papabur/sE1X-10mm/sE1X X Axis Printed Parts/OpenX Carriage (sE1X_15)(1of3).SLDPRT

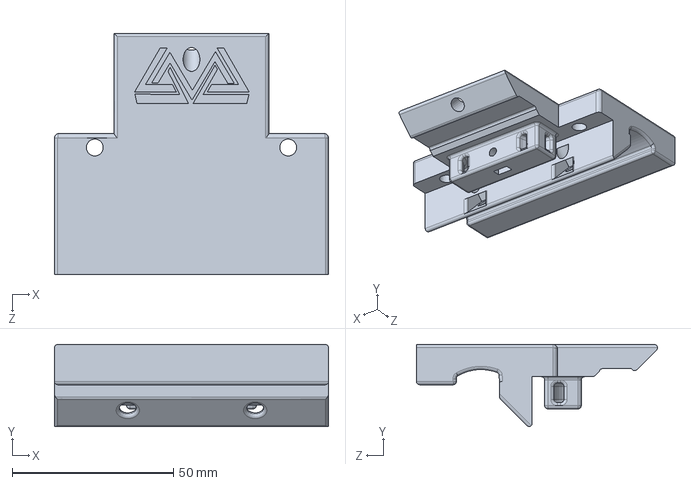
[picture p15: CAD file, 2015-11-26]
sE1X X Axis Printed Parts/OpenX Carriage (sE1X_15)(1of3).SLDPRT
85.0 x 25.5 x 74.8 mm
