papabur/sE1X-10mm/sE1X Y Axis Printed Parts/Printer Supports -sE1X.SLDPRT

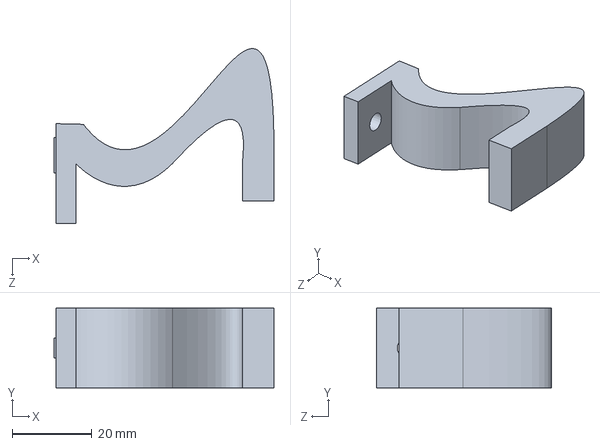
[picture p16: CAD file, 2015-11-09]
sE1X Y Axis Printed Parts/Printer Supports -sE1X.SLDPRT
55.1 x 20.0 x 43.8 mm
