papabur/sE1X-10mm/sE1X Z Axis Printed Parts/5mm threaded rod.SLDPRT

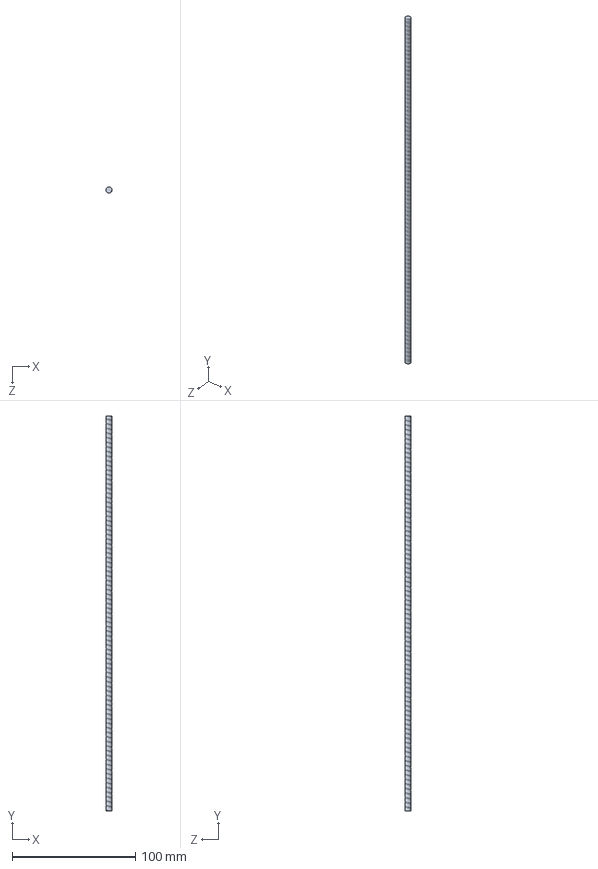
[picture p17: CAD file, 2015-11-19]
sE1X Z Axis Printed Parts/5mm threaded rod.SLDPRT
5.00 x 321.1 x 5.00 mm
