papabur/sE1X-10mm/ChrisM21 10mm star fit.SLDPRT

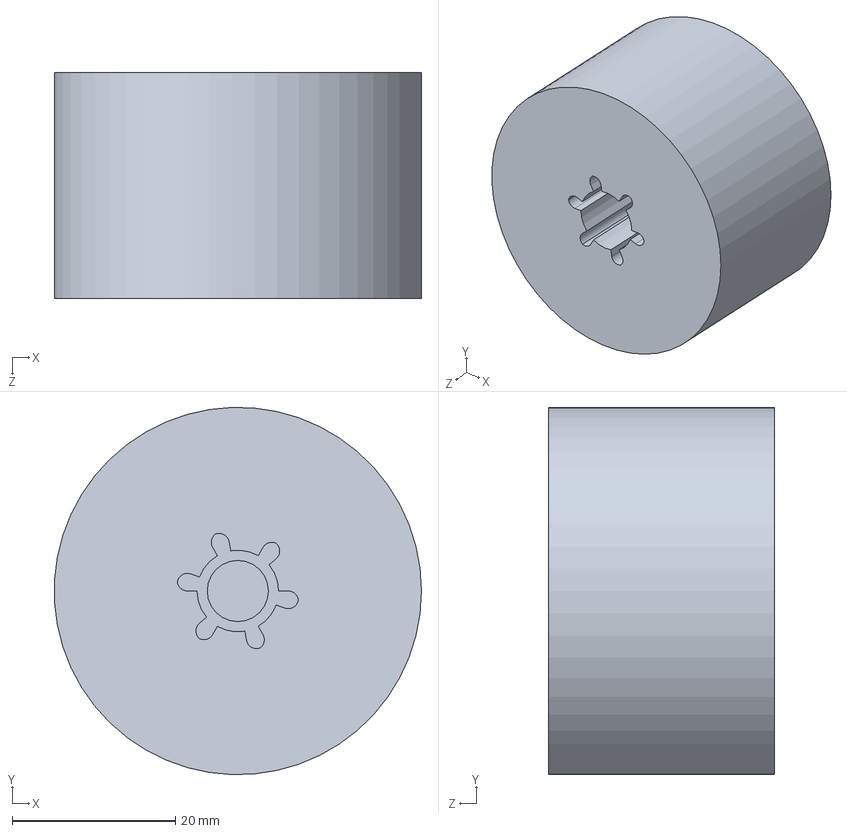
[picture p18: CAD file, 2015-11-09]
ChrisM21 10mm star fit.SLDPRT
45.0 x 45.0 x 27.7 mm
