papabur/sE1X-10mm/i3 Rework/EXTRUDER-IDLER-avec-guide.stl

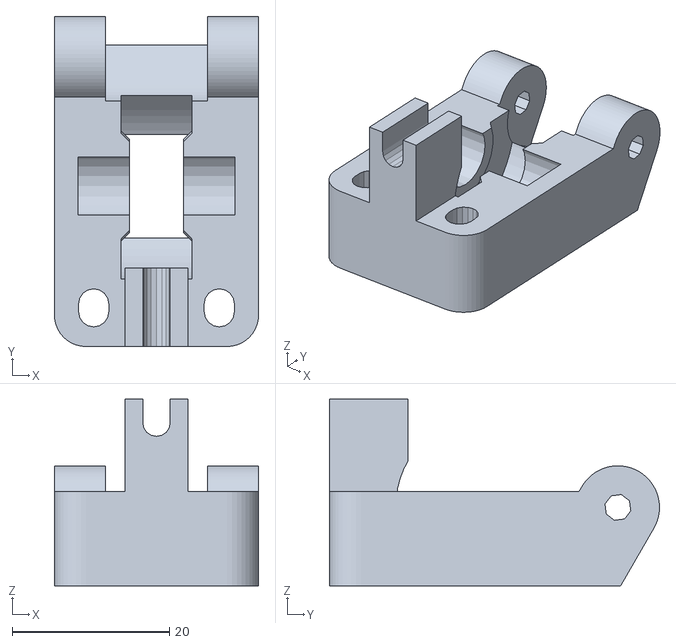
[picture p19: CAD file, 2015-05-26]
i3 Rework/EXTRUDER-IDLER-avec-guide.stl
26.0 x 42.0 x 23.8
