papabur/sE1X-10mm/sE1X E Axis Printed Parts/Airtripper_Bowden_Extruder_BSP_Edition/pipe.stl

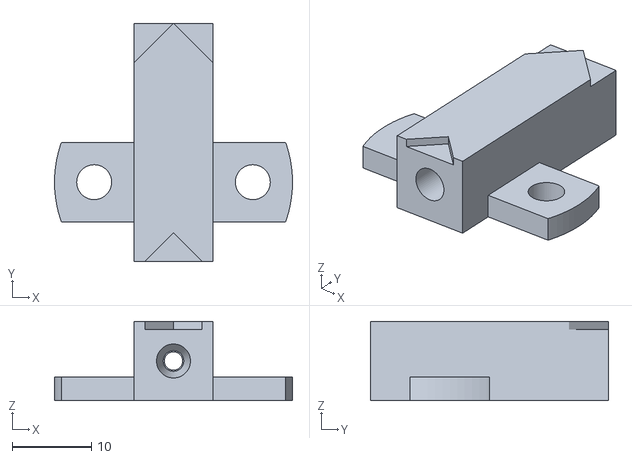
[picture p20: CAD file, 2015-11-26]
sE1X E Axis Printed Parts/Airtripper_Bowden_Extruder_BSP_Edition/pipe.stl
30.0 x 30.0 x 10.0
