papabur/sE1X-10mm/sE1X E Axis Printed Parts/sE1X PSU 2020 mount(unmeasured).SLDPRT

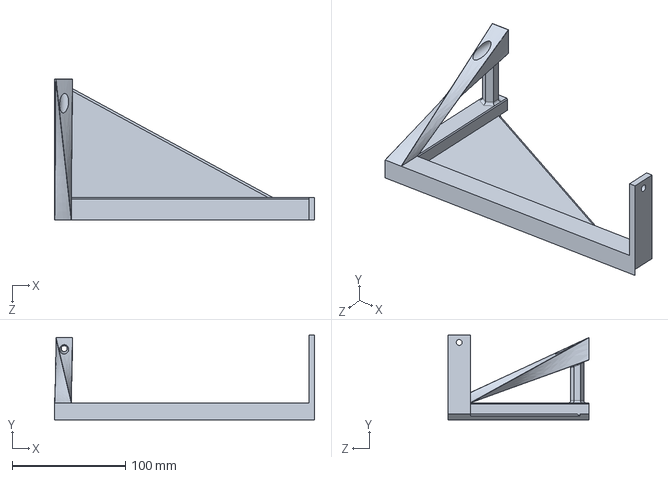
[picture p21: CAD file, 2015-11-09]
sE1X E Axis Printed Parts/sE1X PSU 2020 mount(unmeasured).SLDPRT
230.0 x 75.0 x 125.0 mm
