papabur/sE1X-10mm/sE1X Gantry Supports/sE1X Gantry Support Y Axis brace clamp.SLDPRT

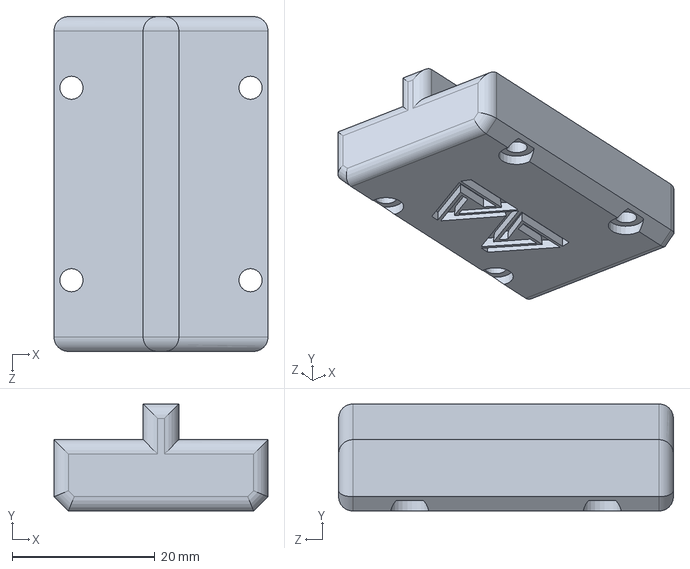
[picture p22: CAD file, 2015-07-30]
sE1X Gantry Supports/sE1X Gantry Support Y Axis brace clamp.SLDPRT
30.0 x 15.0 x 47.0 mm
