papabur/sE1X-10mm/sE1X X Axis Printed Parts/OpenX top bracket(3of3).SLDPRT

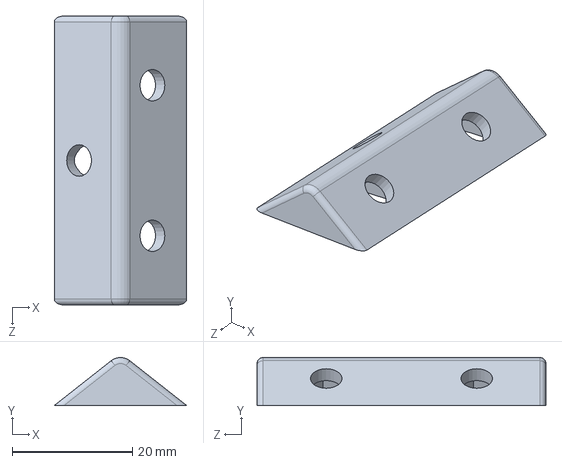
[picture p23: CAD file, 2015-11-26]
sE1X X Axis Printed Parts/OpenX top bracket(3of3).SLDPRT
22.0 x 7.98 x 48.0 mm
