papabur/sE1X-10mm/sE1X Y Axis Printed Parts/605Z Ball bearing.SLDPRT

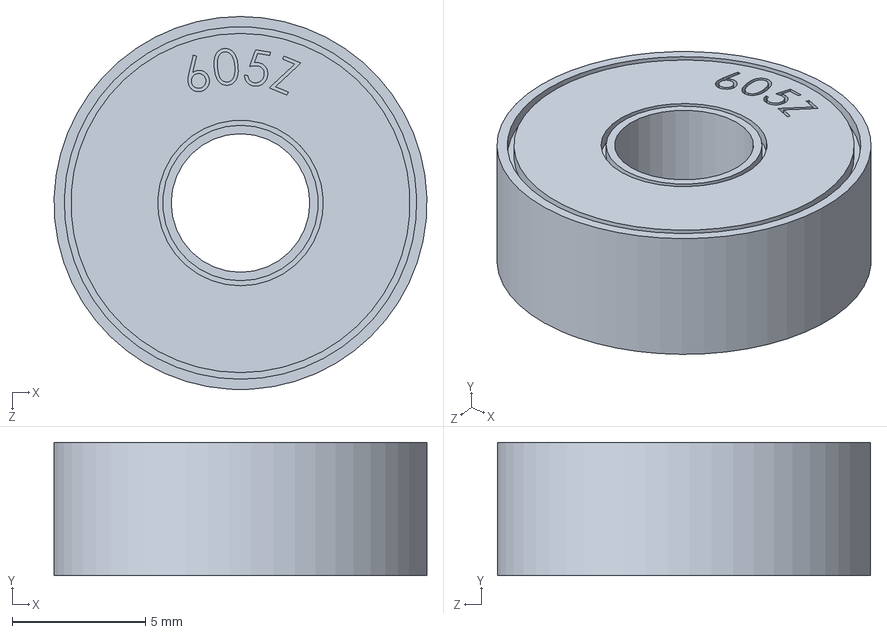
[picture p24: CAD file, 2015-11-09]
sE1X Y Axis Printed Parts/605Z Ball bearing.SLDPRT
14.0 x 5.00 x 14.0 mm
