papabur/sE1X-10mm/sE1X Z Axis Printed Parts/5mm coupler.SLDPRT

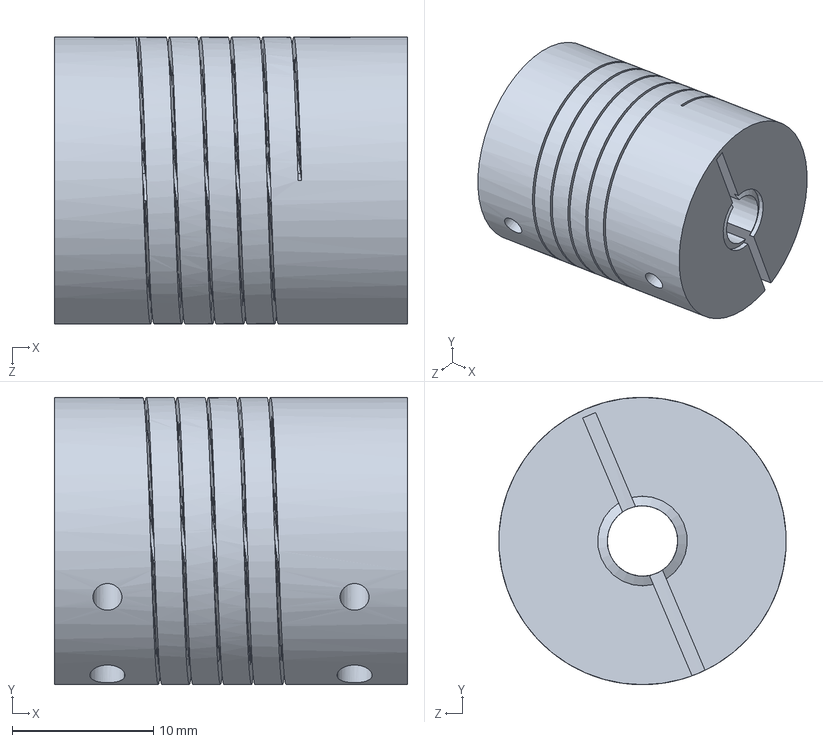
[picture p25: CAD file, 2015-11-19]
sE1X Z Axis Printed Parts/5mm coupler.SLDPRT
25.0 x 20.4 x 20.3 mm
