papabur/sE1X-10mm/i3 Rework/BODY-EXTRUDEUR-WADE-1.75mm-with-support.stl

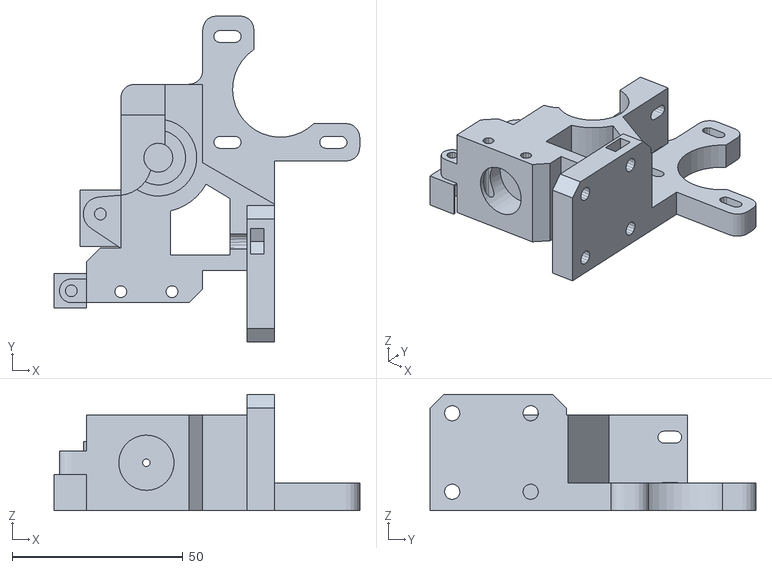
[picture p26: CAD file, 2015-05-26]
i3 Rework/BODY-EXTRUDEUR-WADE-1.75mm-with-support.stl
89.5 x 95.5 x 34.0
