papabur/sE1X-10mm/sE1X E Axis Printed Parts/Airtripper_Bowden_Extruder_BSP_Edition/strut.stl

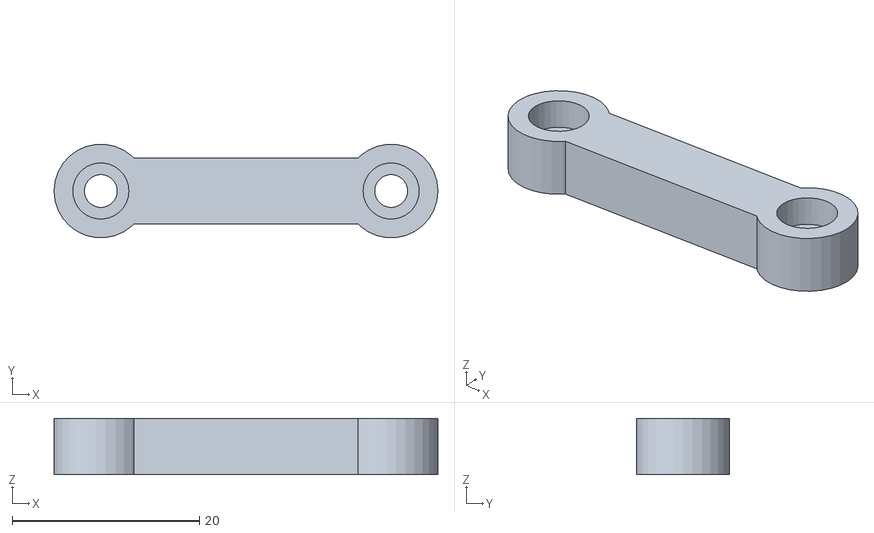
[picture p27: CAD file, 2015-11-26]
sE1X E Axis Printed Parts/Airtripper_Bowden_Extruder_BSP_Edition/strut.stl
41.0 x 9.95 x 6.00
