papabur/sE1X-10mm/sE1X E Axis Printed Parts/sE1X PSU 2020 mount.STL

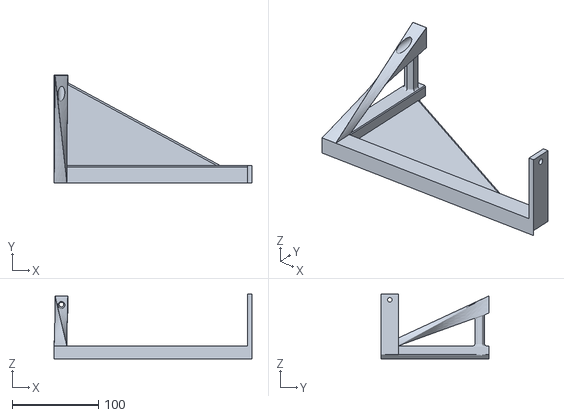
[picture p28: CAD file, 2015-11-09]
sE1X E Axis Printed Parts/sE1X PSU 2020 mount.STL
230.0 x 125.0 x 75.0
