papabur/sE1X-10mm/sE1X Gantry Supports/sE1X Gantry Support Y Axis Brace(L).SLDPRT

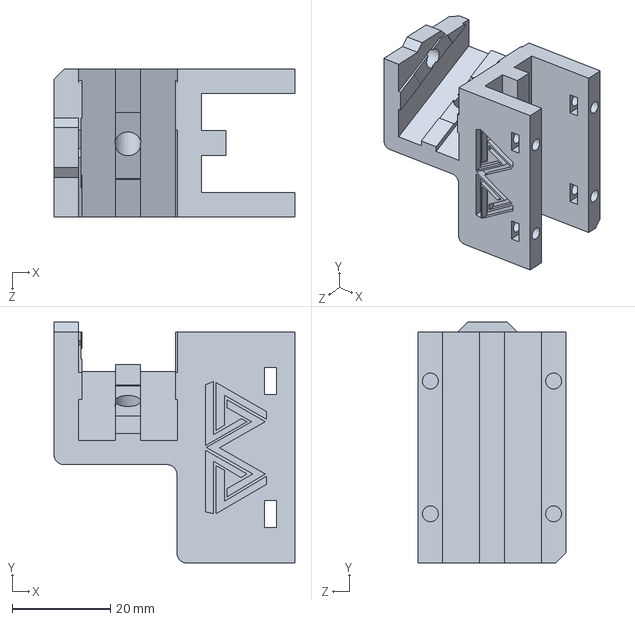
[picture p29: CAD file, 2015-07-30]
sE1X Gantry Supports/sE1X Gantry Support Y Axis Brace(L).SLDPRT
49.0 x 49.0 x 30.0 mm
