papabur/sE1X-10mm/sE1X Y Axis Printed Parts/sE1X OpenY carriage side bracket(x2).SLDPRT

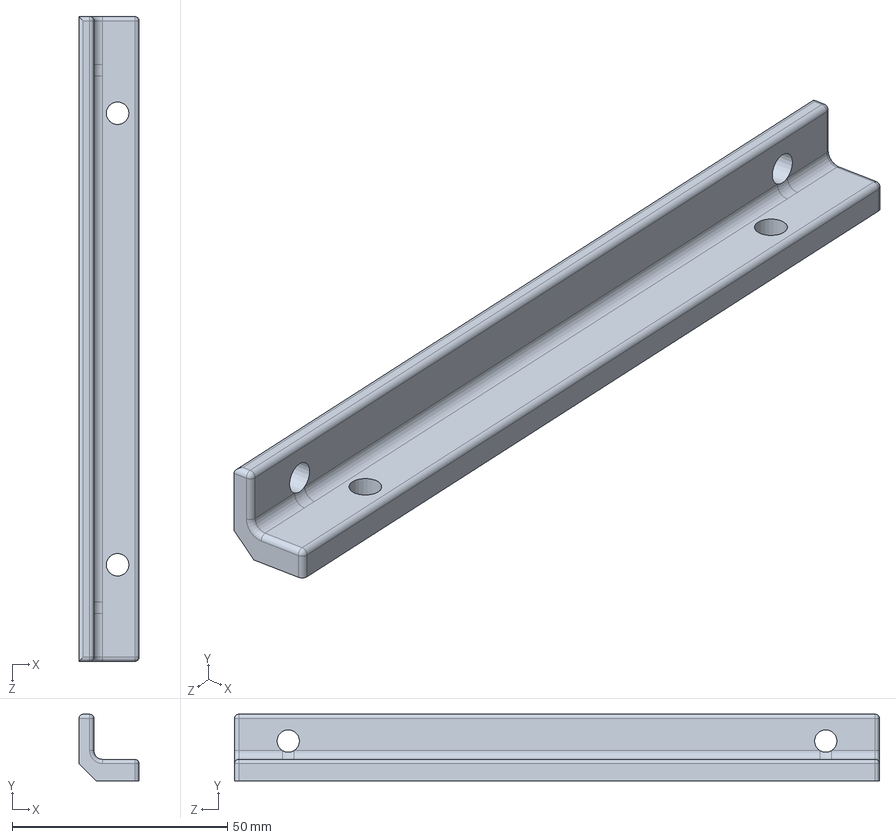
[picture p31: CAD file, 2015-11-09]
sE1X Y Axis Printed Parts/sE1X OpenY carriage side bracket(x2).SLDPRT
14.0 x 15.5 x 150.0 mm
