papabur/sE1X-10mm/sE1X Z Axis Printed Parts/sE1X Z Axis top motor bracket(mirrored).SLDPRT

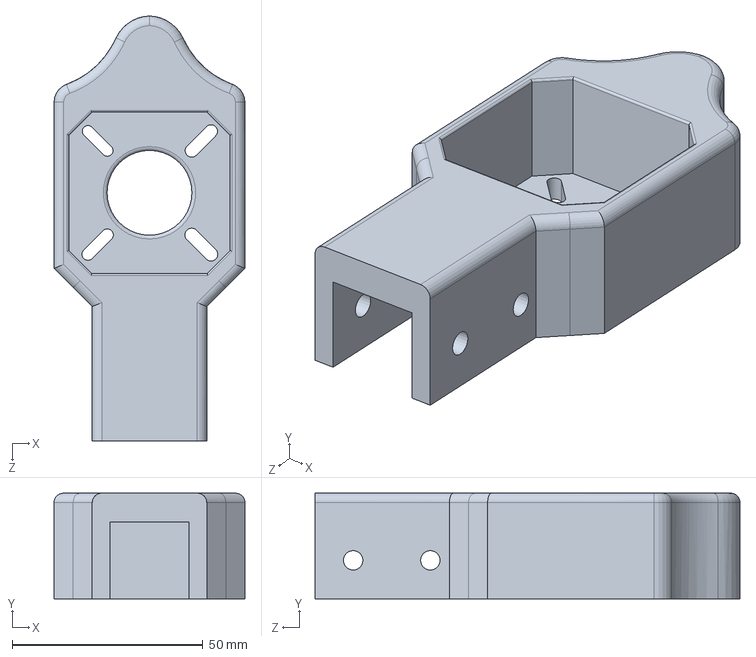
[picture p32: CAD file, 2015-11-09]
sE1X Z Axis Printed Parts/sE1X Z Axis top motor bracket(mirrored).SLDPRT
50.0 x 27.7 x 111.3 mm
