papabur/sE1X-10mm/i3 Rework/WADE-SMALL-GEAR.stl

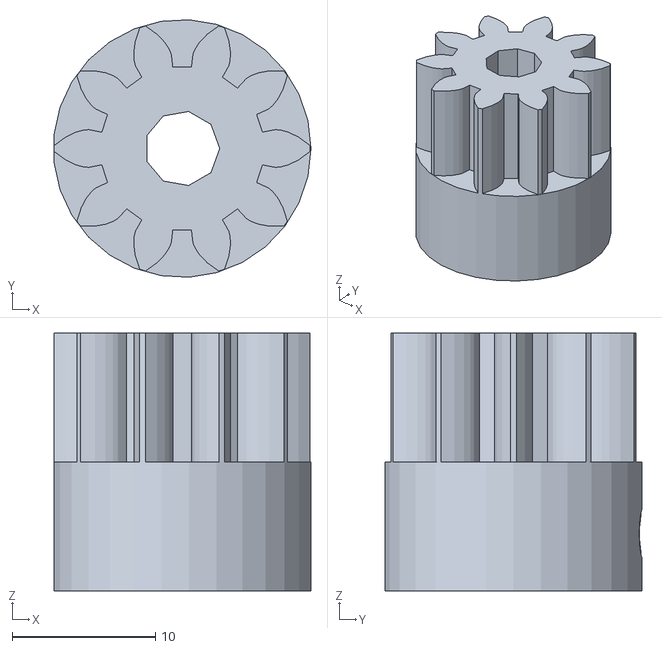
[picture p33: CAD file, 2015-05-26]
i3 Rework/WADE-SMALL-GEAR.stl
17.9 x 18.0 x 18.0
