papabur/sE1X-10mm/sE1X E Axis Printed Parts/Airtripper_Bowden_Extruder_BSP_Edition/air-bsp.stl

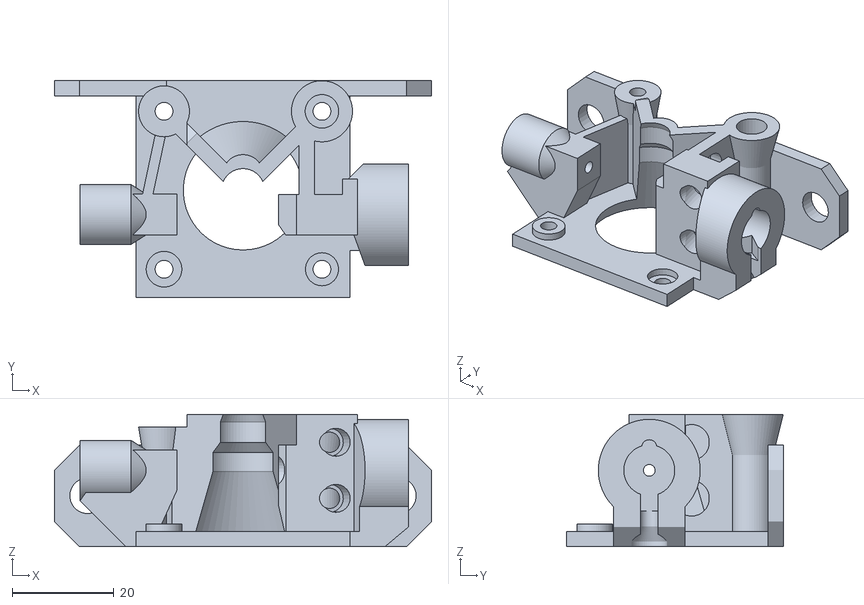
[picture p35: CAD file, 2015-11-26]
sE1X E Axis Printed Parts/Airtripper_Bowden_Extruder_BSP_Edition/air-bsp.stl
74.0 x 42.5 x 26.0
