papabur/sE1X-10mm/sE1X Y Axis Printed Parts/sE1X Y idler t-bracket.SLDPRT

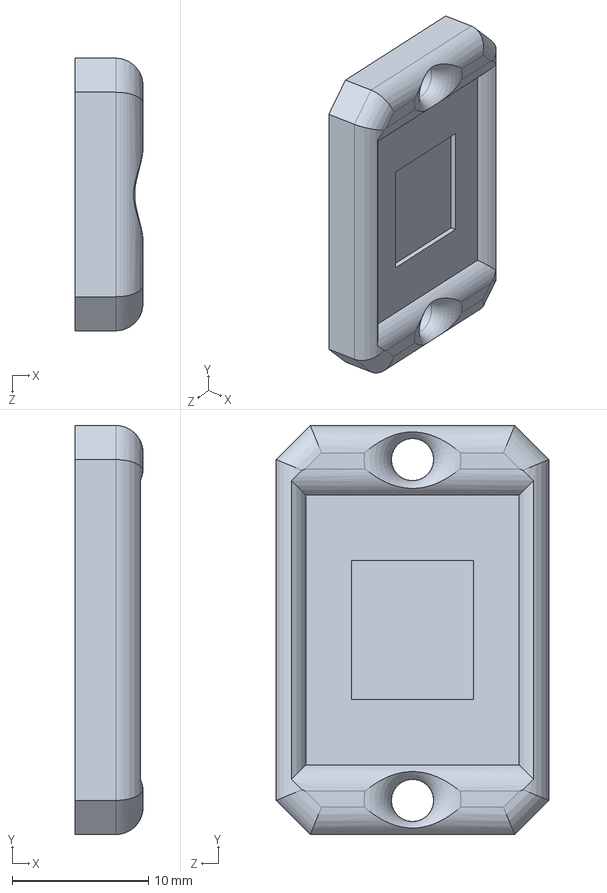
[picture p36: CAD file, 2015-11-09]
sE1X Y Axis Printed Parts/sE1X Y idler t-bracket.SLDPRT
5.00 x 30.0 x 20.0 mm
