papabur/sE1X-10mm/i3 Rework/WADE-BIG-GEAR.stl

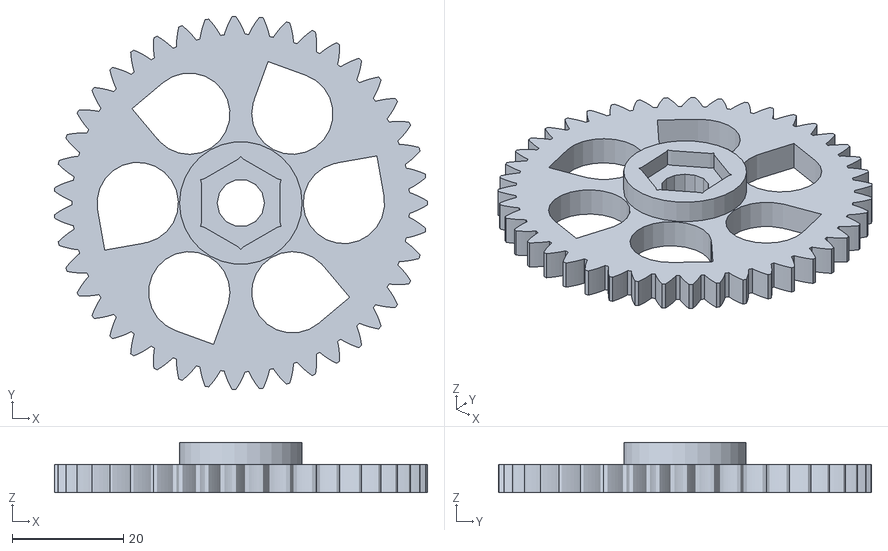
[picture p37: CAD file, 2015-05-26]
i3 Rework/WADE-BIG-GEAR.stl
66.9 x 67.0 x 9.00
