papabur/sE1X-10mm/sE1X E Axis Printed Parts/Airtripper swivel mount.SLDPRT

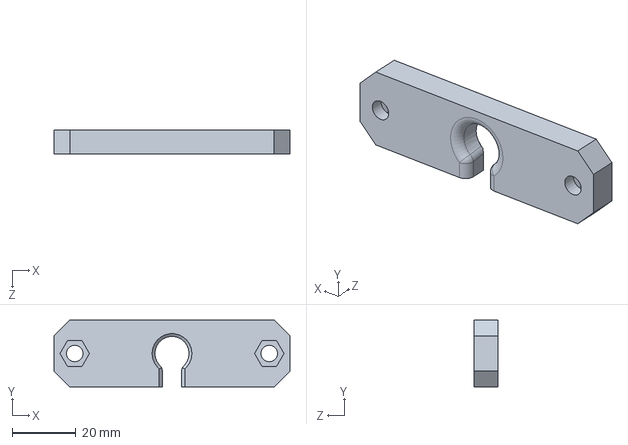
[picture p38: CAD file, 2015-08-09]
sE1X E Axis Printed Parts/Airtripper swivel mount.SLDPRT
74.0 x 21.0 x 7.50 mm
