papabur/sE1X-10mm/sE1X X Axis Printed Parts/OpenX b90-bracket(2of3).SLDPRT

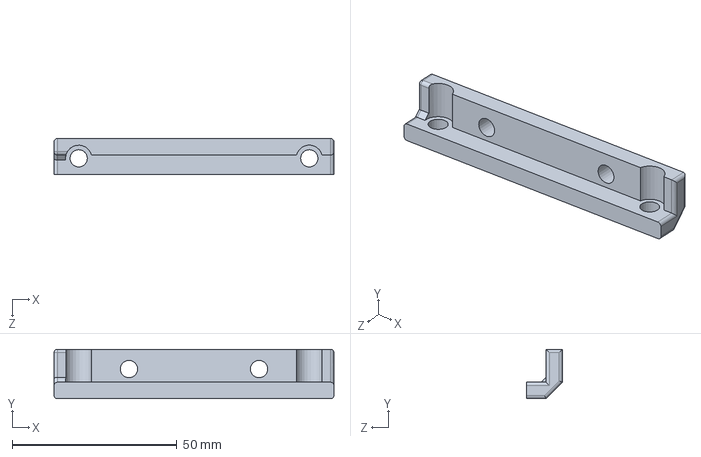
[picture p39: CAD file, 2015-11-26]
sE1X X Axis Printed Parts/OpenX b90-bracket(2of3).SLDPRT
85.0 x 15.0 x 10.9 mm
