papabur/sE1X-10mm/sE1X Y Axis Printed Parts/sE1X Y idler.SLDPRT

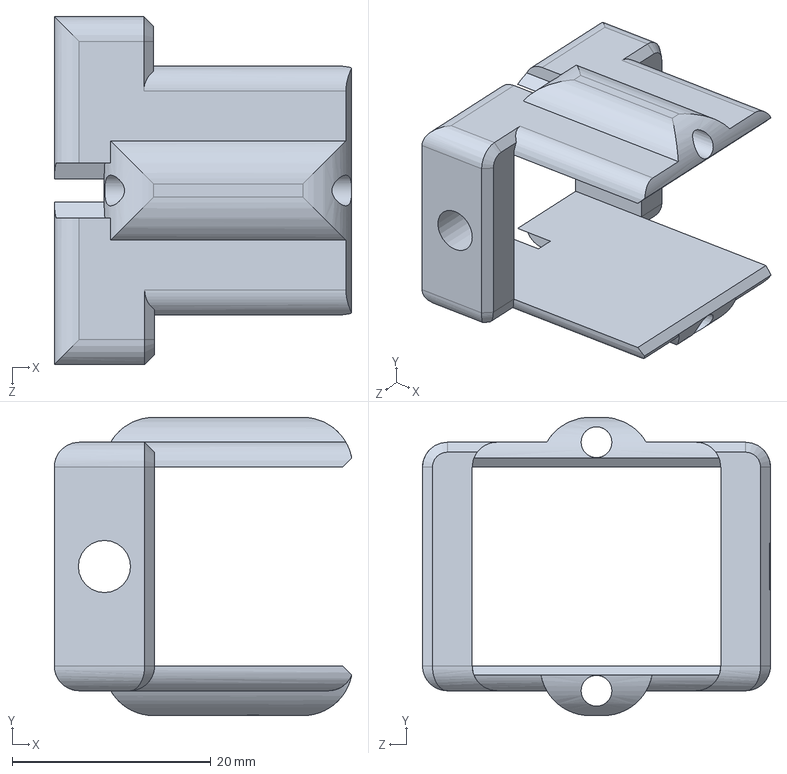
[picture p40: CAD file, 2015-11-09]
sE1X Y Axis Printed Parts/sE1X Y idler.SLDPRT
29.9 x 30.0 x 35.0 mm
