papabur/sE1X-10mm/sE1X Z Axis Printed Parts/sE1X Z Axis top motor mount.STL

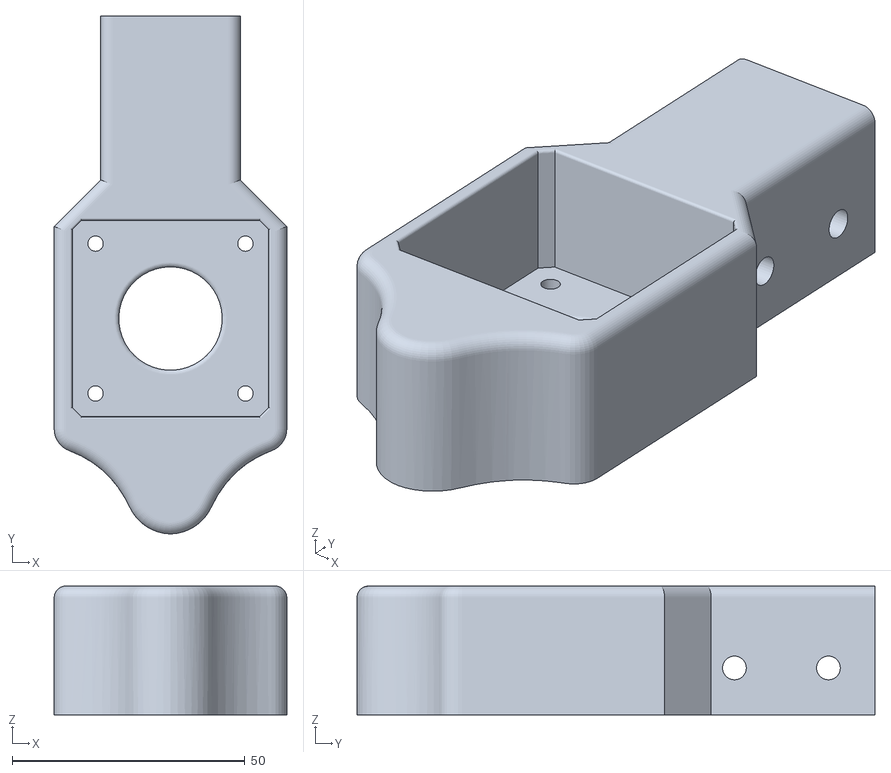
[picture p41: CAD file, 2015-11-09]
sE1X Z Axis Printed Parts/sE1X Z Axis top motor mount.STL
50.0 x 111.3 x 27.7
