papabur/sE1X-10mm/sE1X E Axis Printed Parts/AO_Fan_Mount_v1.2.STL

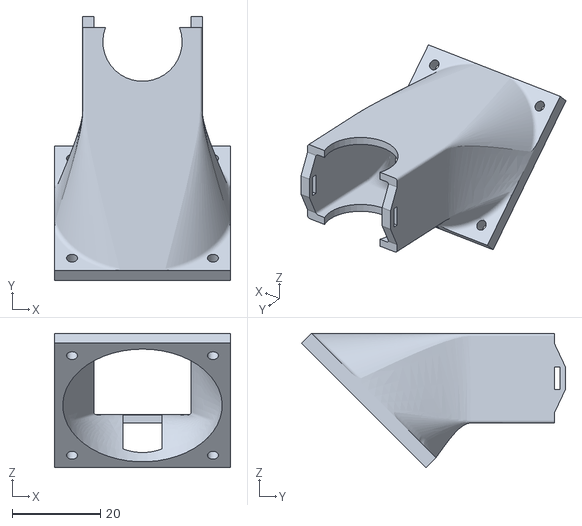
[picture p42: CAD file, 2015-06-04]
sE1X E Axis Printed Parts/AO_Fan_Mount_v1.2.STL
40.0 x 59.9 x 30.5
