papabur/sE1X-10mm/sE1X X Axis Printed Parts/OpenX Hotend Bracket(HJ-M).SLDPRT

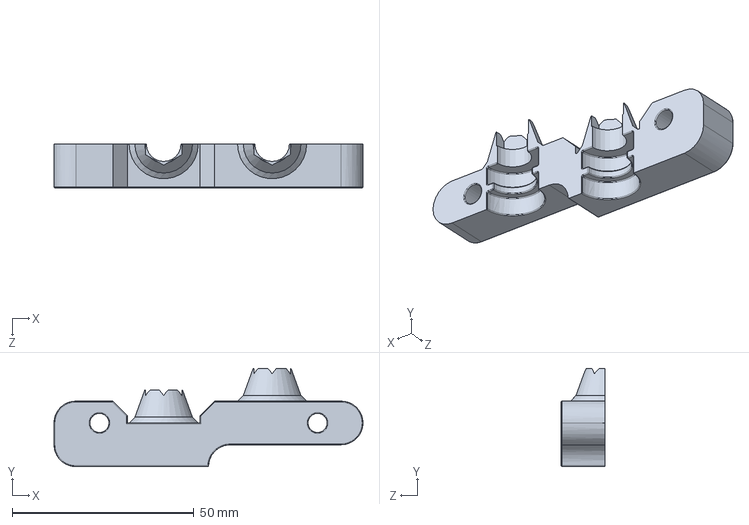
[picture p43: CAD file, 2015-11-26]
sE1X X Axis Printed Parts/OpenX Hotend Bracket(HJ-M).SLDPRT
85.0 x 27.0 x 12.0 mm
