papabur/sE1X-10mm/sE1X Y Axis Printed Parts/sE1X OpenY carriage.SLDPRT

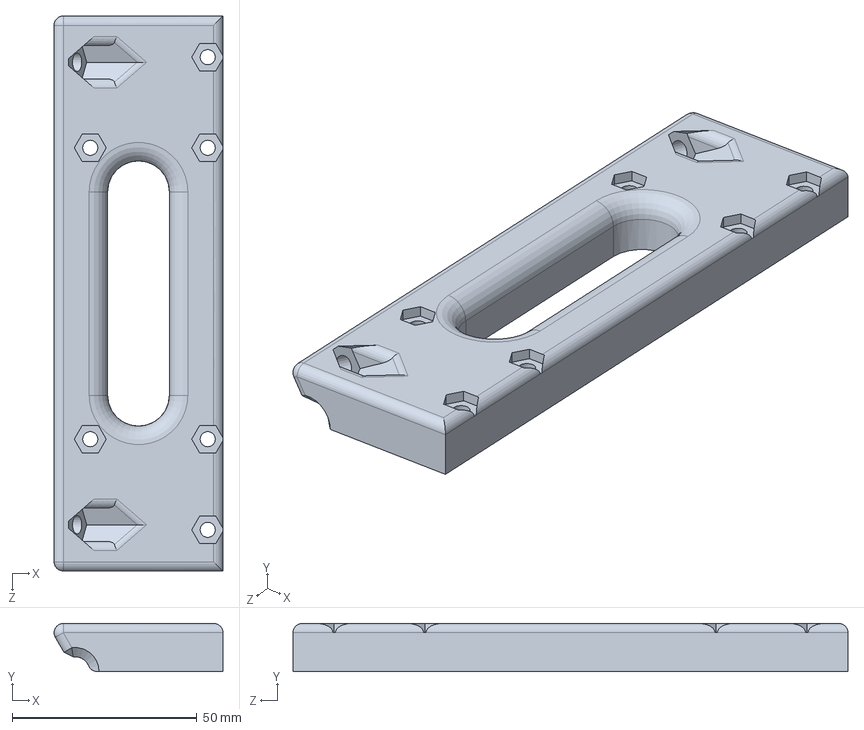
[picture p44: CAD file, 2015-11-09]
sE1X Y Axis Printed Parts/sE1X OpenY carriage.SLDPRT
45.7 x 13.0 x 150.0 mm
