papabur/sE1X-10mm/sE1X Z Axis Printed Parts/sE1X Gantry 150mm 2020 extrusion extension with airtripper swivel.SLDPRT

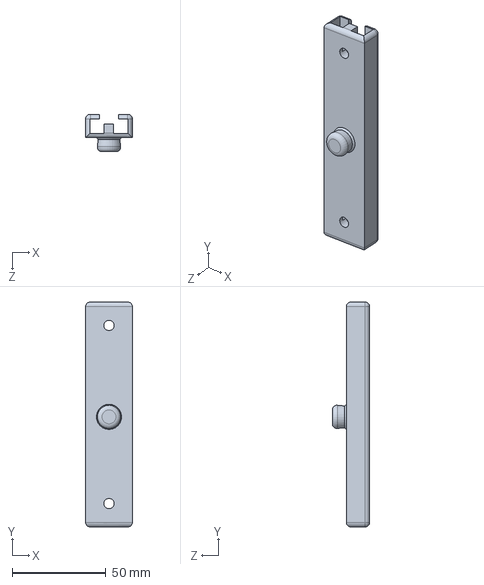
[picture p45: CAD file, 2015-08-09]
sE1X Z Axis Printed Parts/sE1X Gantry 150mm 2020 extrusion extension with airtripper swivel.SLDPRT
25.0 x 120.0 x 20.0 mm
