papabur/sE1X-10mm/sE1X X Axis Printed Parts/OpenX Dual hotend backplate.SLDPRT

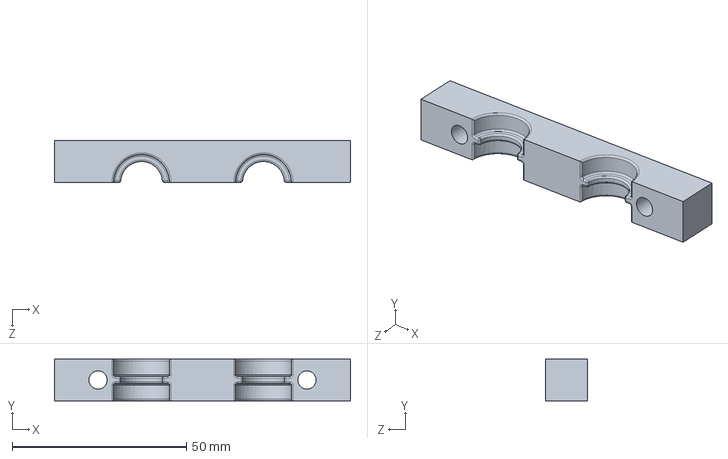
[picture p46: CAD file, 2015-11-26]
sE1X X Axis Printed Parts/OpenX Dual hotend backplate.SLDPRT
85.0 x 12.0 x 12.0 mm
