papabur/sE1X-10mm/sE1X Z Axis Printed Parts/sE1X Z Axis bottom bracket clamp.SLDPRT

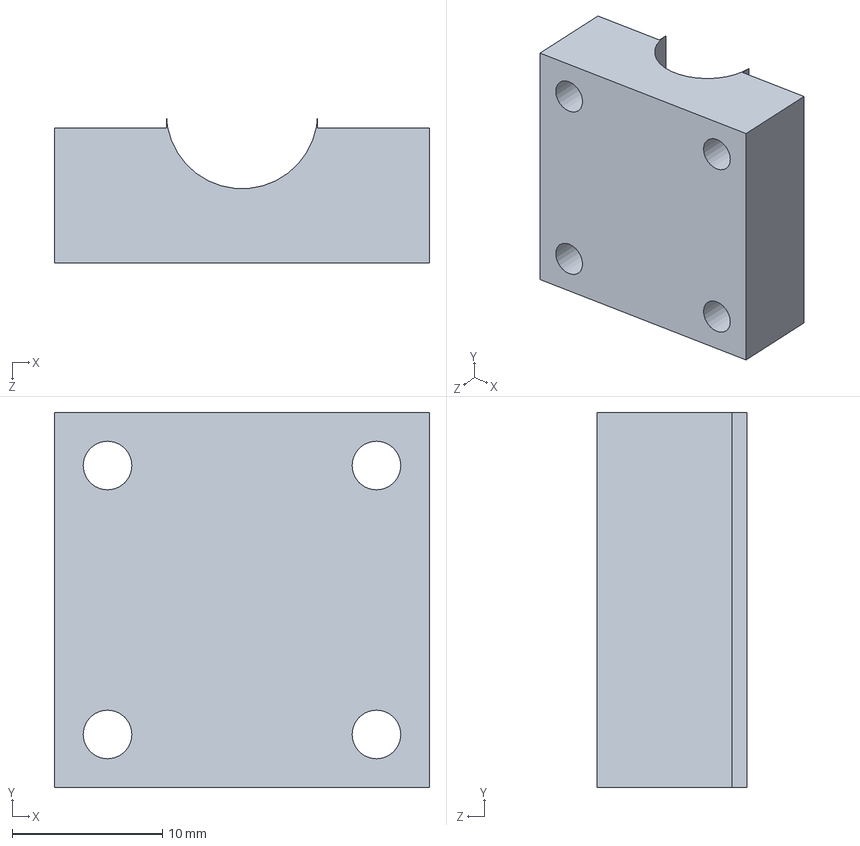
[picture p47: CAD file, 2015-07-30]
sE1X Z Axis Printed Parts/sE1X Z Axis bottom bracket clamp.SLDPRT
25.0 x 25.0 x 10.0 mm
