papabur/sE1X-10mm/sE1X X Axis Printed Parts/SE1X 10mm carriage(BOWDEN).SLDPRT

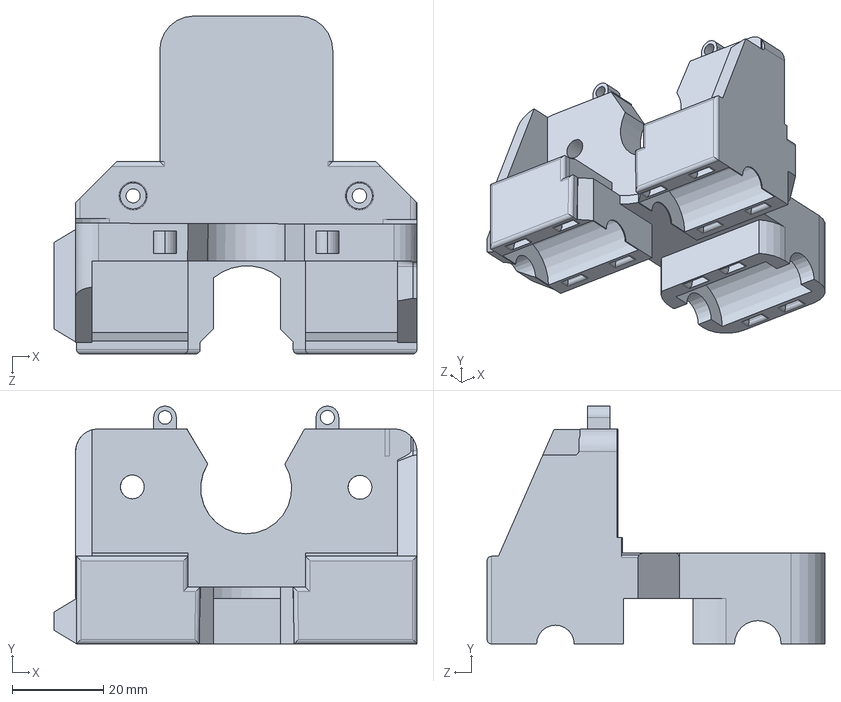
[picture p48: CAD file, 2015-11-19]
sE1X X Axis Printed Parts/SE1X 10mm carriage(BOWDEN).SLDPRT
79.7 x 52.3 x 74.2 mm
