papabur/sE1X-10mm/sE1X Y Axis Printed Parts/Y_Idler_Tensioner arm only.stl

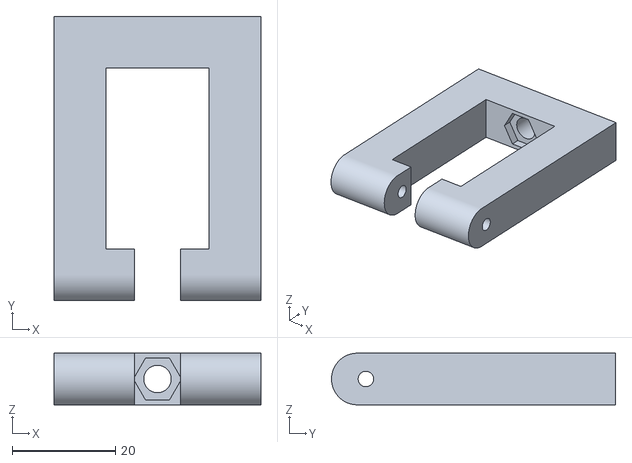
[picture p49: CAD file, 2015-11-09]
sE1X Y Axis Printed Parts/Y_Idler_Tensioner arm only.stl
40.0 x 55.0 x 10.0
