papabur/sE1X-10mm/sE1X Z Axis Printed Parts/sE1X Z Axis bottom bracket.SLDPRT

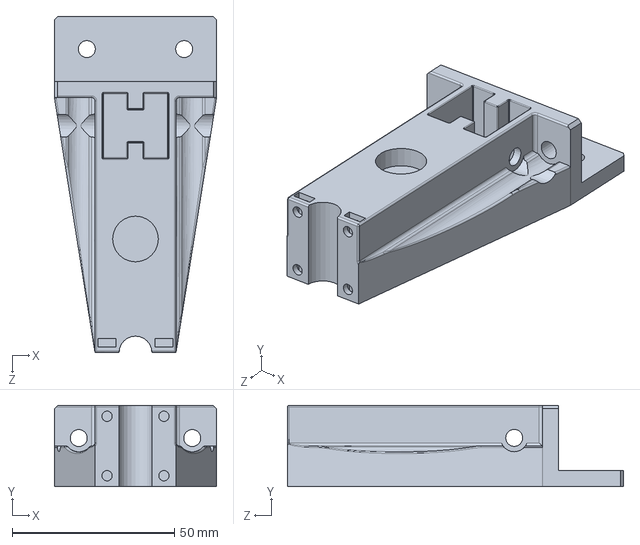
[picture p50: CAD file, 2015-07-30]
sE1X Z Axis Printed Parts/sE1X Z Axis bottom bracket.SLDPRT
50.0 x 25.0 x 103.6 mm
