papabur/sE1X-10mm/sE1X X Axis Printed Parts/605ZZ Bearing.SLDPRT

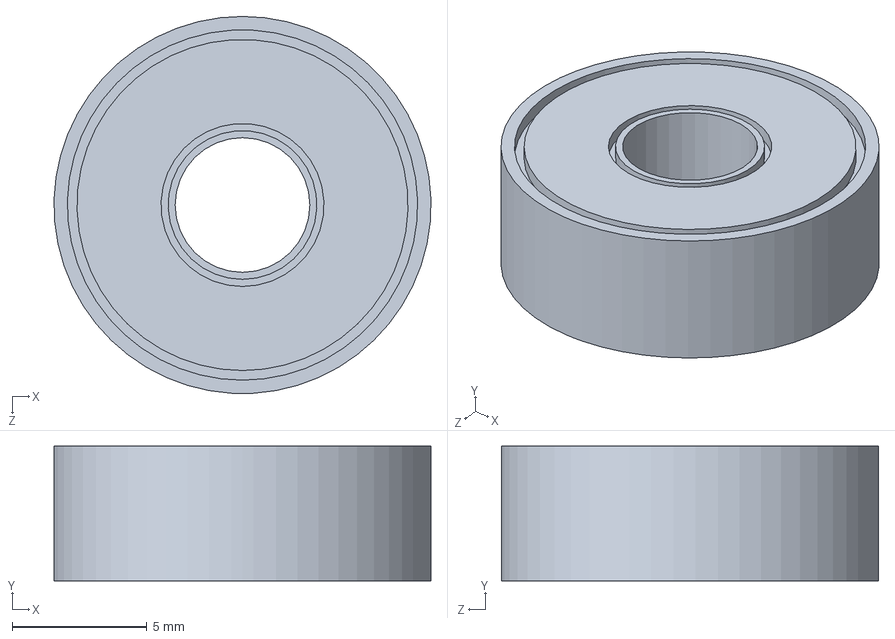
[picture p51: CAD file, 2015-11-19]
sE1X X Axis Printed Parts/605ZZ Bearing.SLDPRT
14.0 x 5.00 x 14.0 mm
