papabur/sE1X-10mm/sE1X Z Axis Printed Parts/2020 Extrusion.SLDPRT

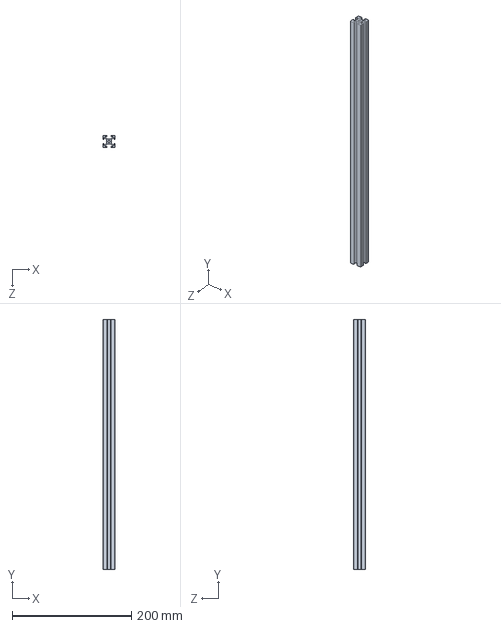
[picture p52: CAD file, 2015-07-13]
sE1X Z Axis Printed Parts/2020 Extrusion.SLDPRT
20.0 x 420.0 x 20.0 mm
