papabur/sE1X-10mm/sE1X Y Axis Printed Parts/(x4)sE1X Y axis 10mm smooth rod holders.stl

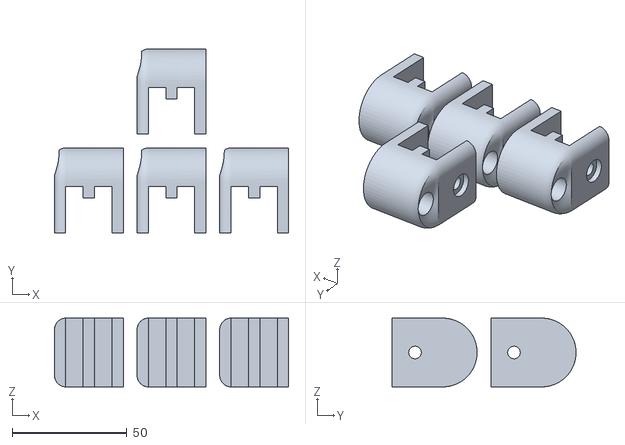
[picture p54: CAD file, 2015-11-09]
sE1X Y Axis Printed Parts/(x4)sE1X Y axis 10mm smooth rod holders.stl
102.0 x 80.2 x 30.0
