papabur/sE1X-10mm/sE1X Z Axis Printed Parts/sE1X Gantry 150mm 2020 extrusion extension.SLDPRT

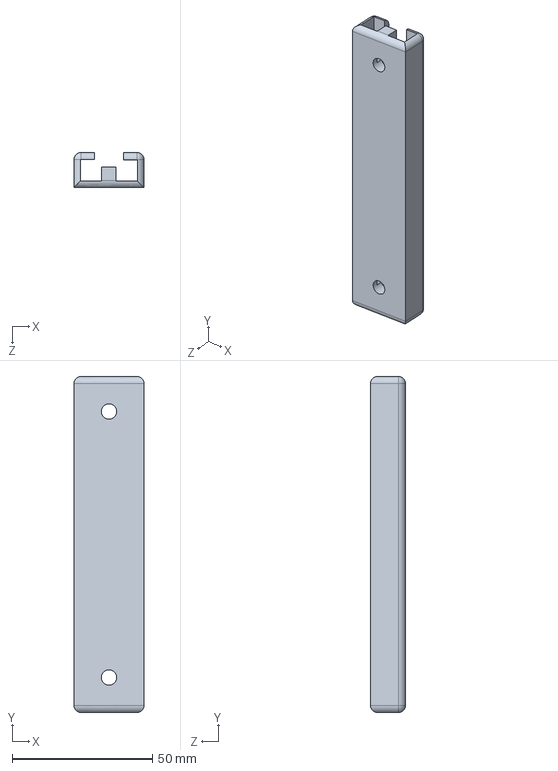
[picture p55: CAD file, 2015-06-28]
sE1X Z Axis Printed Parts/sE1X Gantry 150mm 2020 extrusion extension.SLDPRT
25.0 x 120.0 x 12.5 mm
