papabur/sE1X-10mm/sE1X X Axis Printed Parts/sE1X 465mm 10mm smooth rod.SLDPRT

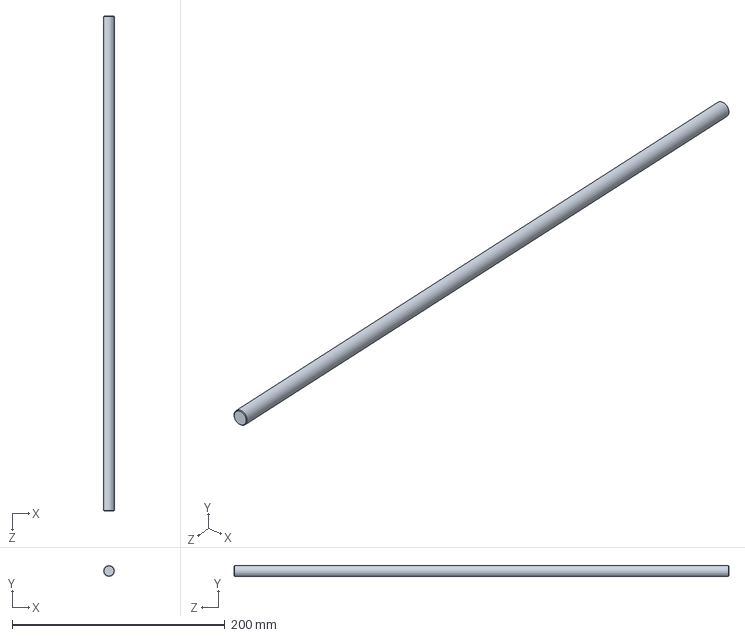
[picture p56: CAD file, 2015-11-19]
sE1X X Axis Printed Parts/sE1X 465mm 10mm smooth rod.SLDPRT
10.0 x 10.0 x 465.0 mm
