papabur/sE1X-10mm/sE1X Y Axis Printed Parts/sE1X heated bed corners.STL

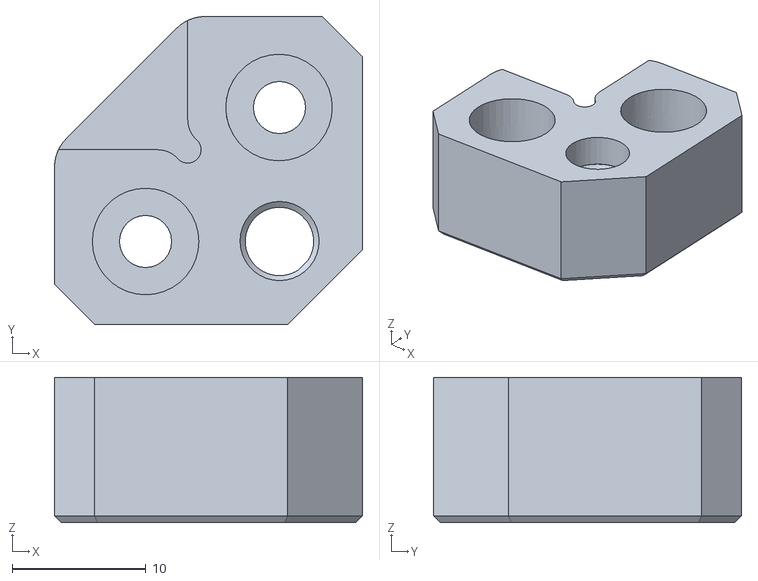
[picture p57: CAD file, 2015-11-09]
sE1X Y Axis Printed Parts/sE1X heated bed corners.STL
23.0 x 23.0 x 10.9
