papabur/sE1X-10mm/sE1X Y Axis Printed Parts/sE1X Y motor mount.SLDPRT

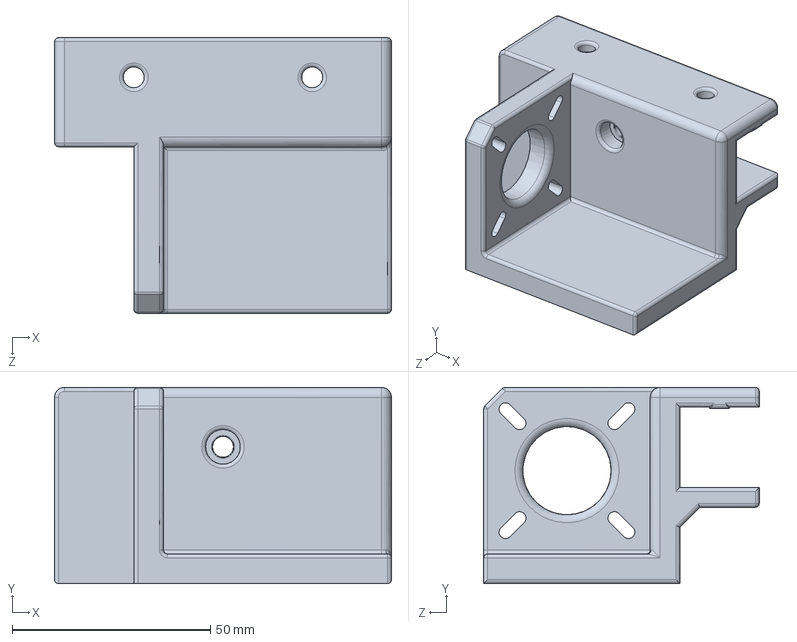
[picture p58: CAD file, 2015-11-09]
sE1X Y Axis Printed Parts/sE1X Y motor mount.SLDPRT
85.0 x 49.5 x 69.5 mm
