papabur/sE1X-10mm/sE1X X Axis Printed Parts/370mm X axis 2020 extrusion.SLDPRT

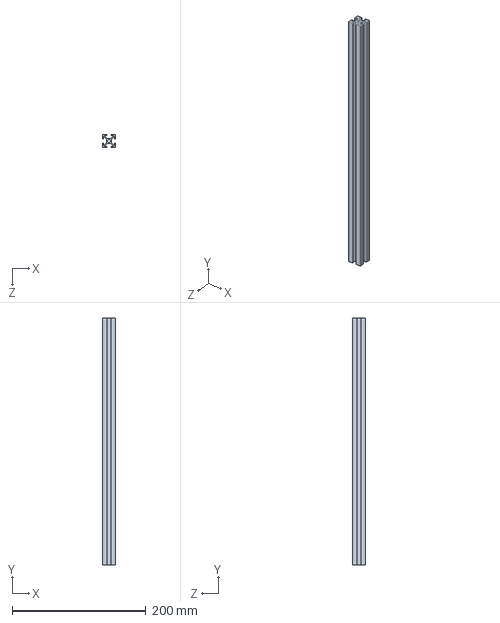
[picture p59: CAD file, 2015-11-19]
sE1X X Axis Printed Parts/370mm X axis 2020 extrusion.SLDPRT
20.0 x 370.0 x 20.0 mm
