papabur/sE1X-10mm/sE1X Y Axis Printed Parts/sE1X Y belt gripper clamp.SLDPRT

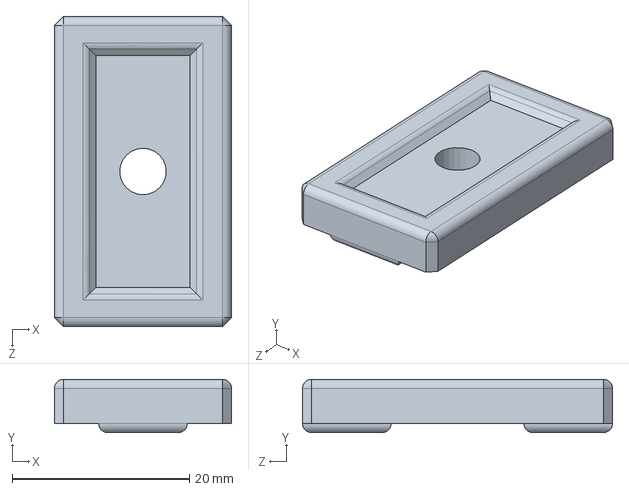
[picture p60: CAD file, 2015-11-09]
sE1X Y Axis Printed Parts/sE1X Y belt gripper clamp.SLDPRT
20.0 x 6.00 x 35.0 mm
