papabur/sE1X-10mm/sE1X X Axis Printed Parts/sE1X X Idler belt tensioner.SLDPRT

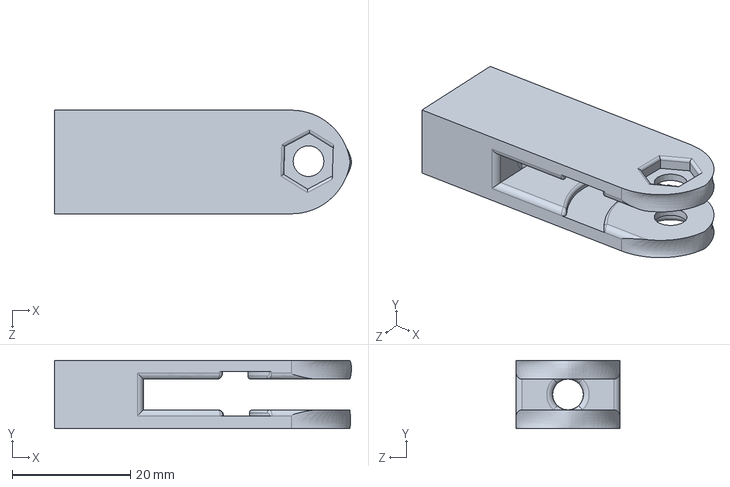
[picture p61: CAD file, 2015-11-09]
sE1X X Axis Printed Parts/sE1X X Idler belt tensioner.SLDPRT
50.2 x 11.5 x 17.5 mm
