papabur/sE1X-10mm/sE1X X Axis Printed Parts/sE1X X Axis Motor end.SLDPRT

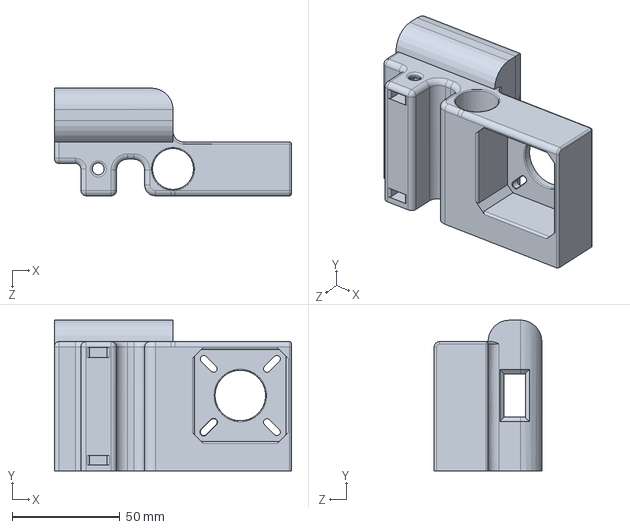
[picture p62: CAD file, 2015-11-09]
sE1X X Axis Printed Parts/sE1X X Axis Motor end.SLDPRT
110.0 x 70.0 x 50.0 mm
