papabur/sE1X-10mm/sE1X Y Axis Printed Parts/Y_Axis_10mm_Smooth_Rod_Holder_-_4x.stl

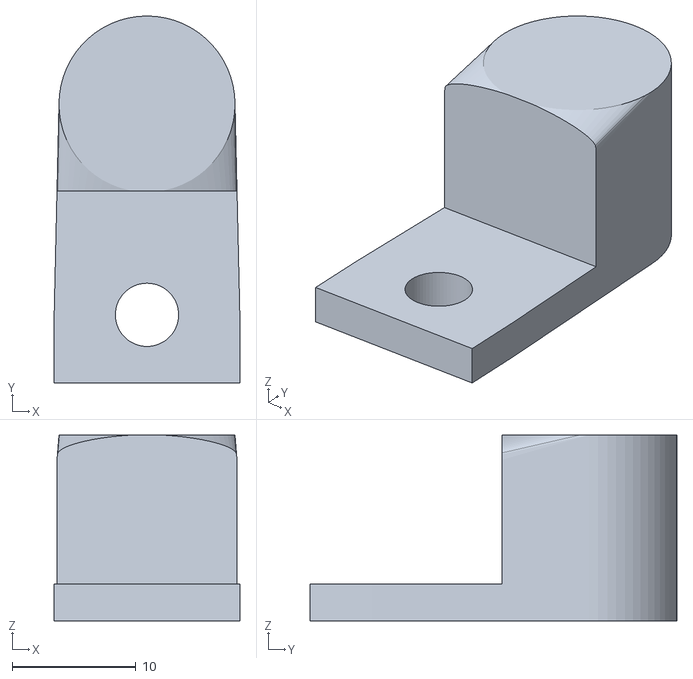
[picture p63: CAD file, 2015-08-31]
sE1X Y Axis Printed Parts/Y_Axis_10mm_Smooth_Rod_Holder_-_4x.stl
15.0 x 29.6 x 15.0
