papabur/sE1X-10mm/sE1X X Axis Printed Parts/SE1X 10mm carriage(BOWDEN) with belt brackets.stl

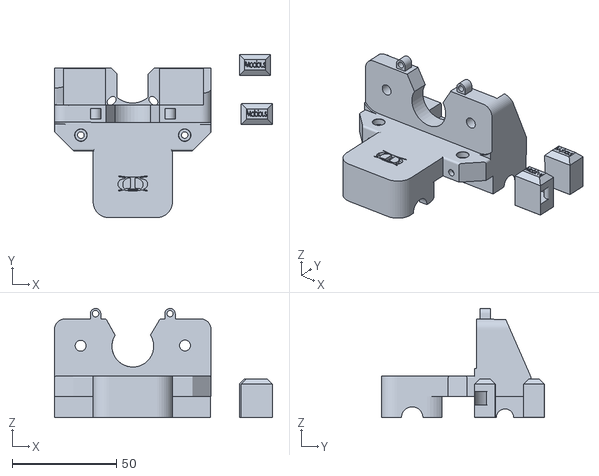
[picture p64: CAD file, 2015-11-09]
sE1X X Axis Printed Parts/SE1X 10mm carriage(BOWDEN) with belt brackets.stl
104.4 x 78.2 x 52.3
