papabur/sE1X-10mm/sE1X Y Axis Printed Parts/Printer_Support_-_4x.stl

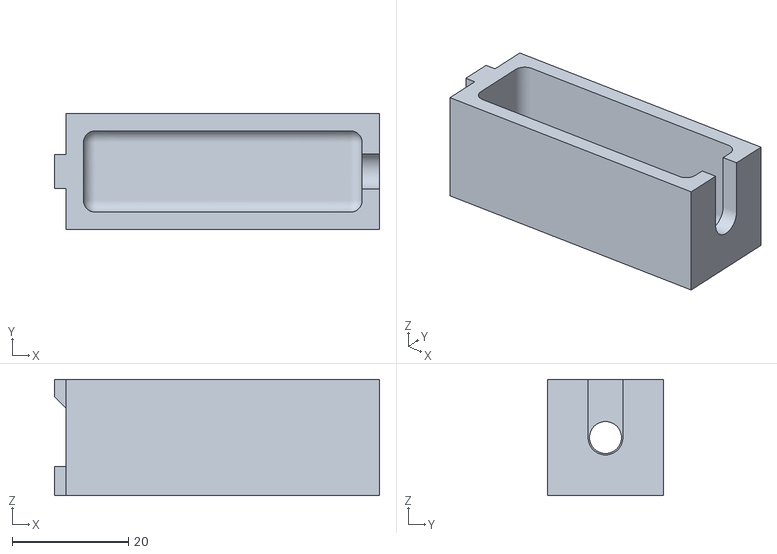
[picture p65: CAD file, 2015-08-31]
sE1X Y Axis Printed Parts/Printer_Support_-_4x.stl
56.0 x 20.0 x 20.0
