papabur/sE1X-10mm/sE1X X Axis Printed Parts/sE1X X idler end.SLDPRT

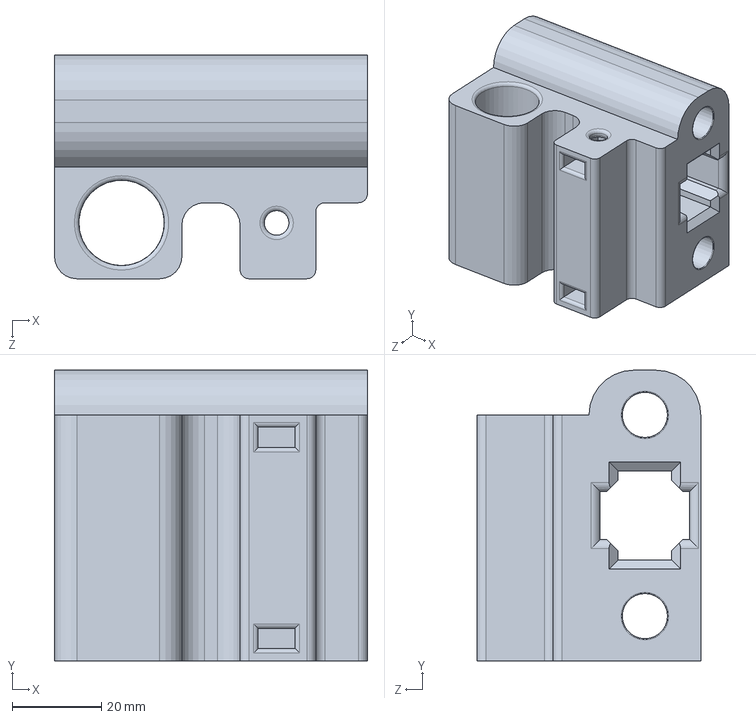
[picture p66: CAD file, 2015-11-09]
sE1X X Axis Printed Parts/sE1X X idler end.SLDPRT
70.0 x 65.0 x 50.0 mm
