papabur/sE1X-10mm/sE1X Y Axis Printed Parts/Y_Idler_With_Tensioner.stl

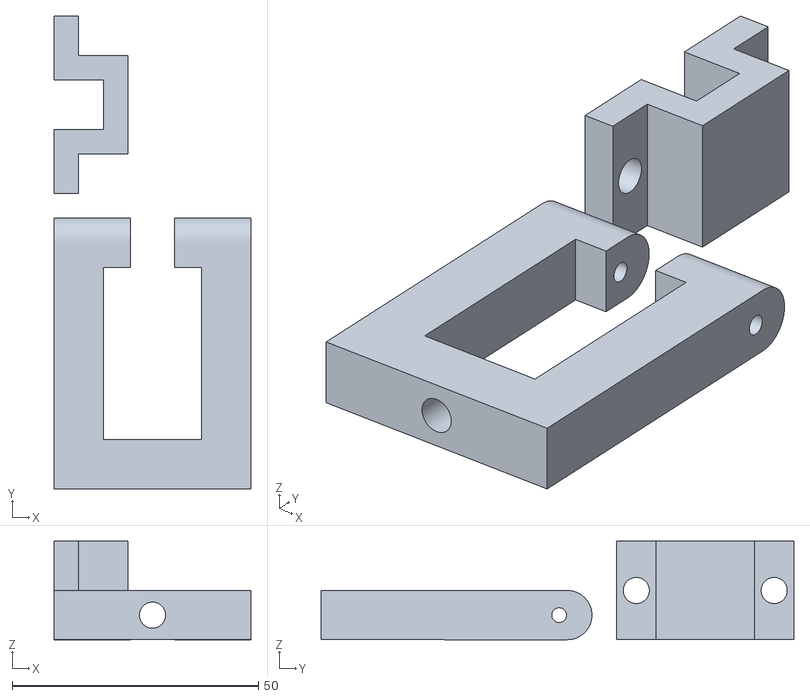
[picture p67: CAD file, 2015-08-31]
sE1X Y Axis Printed Parts/Y_Idler_With_Tensioner.stl
40.0 x 96.0 x 20.0
