papabur/sE1X-10mm/sE1X X Axis Printed Parts/sE1X 10mm extruder belt bracket mirrored.SLDPRT

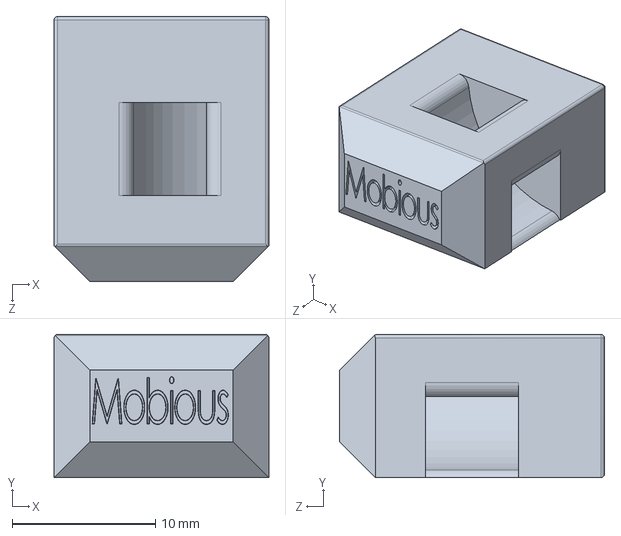
[picture p68: CAD file, 2015-08-23]
sE1X X Axis Printed Parts/sE1X 10mm extruder belt bracket mirrored.SLDPRT
15.0 x 10.0 x 18.5 mm
