papabur/sE1X-10mm/sE1X Y Axis Printed Parts/Y_Axis_Motor_Block_-_1x.stl

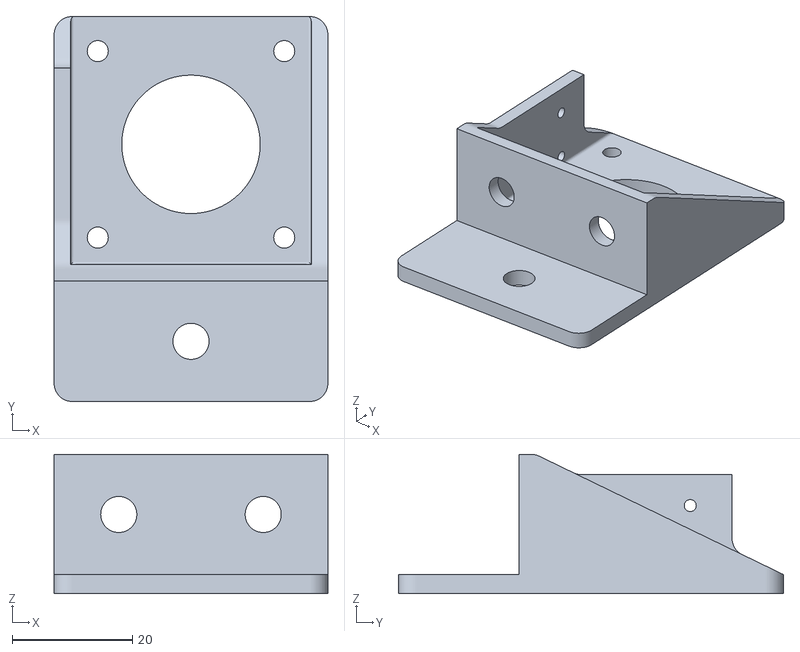
[picture p69: CAD file, 2015-08-31]
sE1X Y Axis Printed Parts/Y_Axis_Motor_Block_-_1x.stl
45.5 x 64.0 x 23.2
