papabur/sE1X-10mm/sE1X Y Axis Printed Parts/lulzbot-bearing_holder_v1.1.b.stl

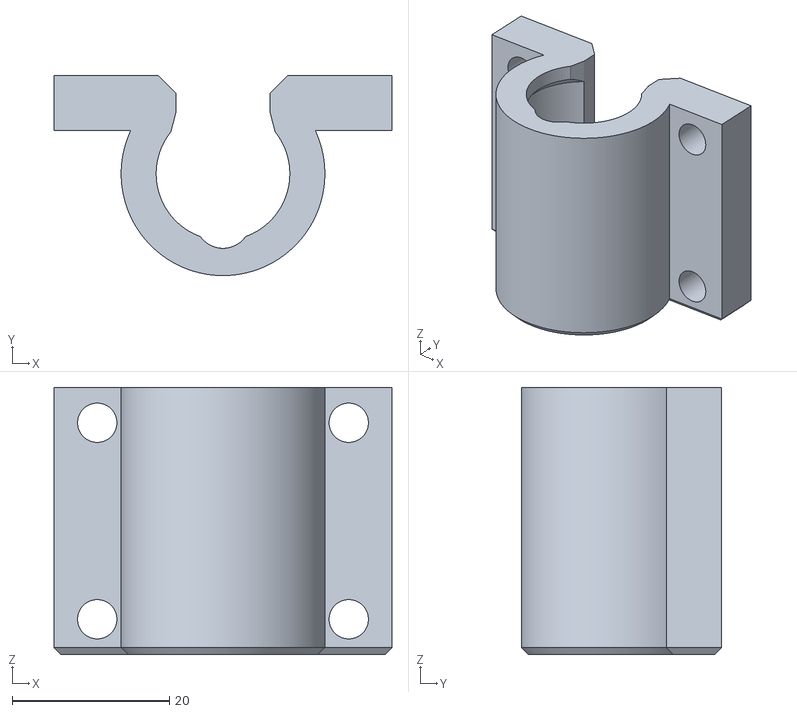
[picture p70: CAD file, 2015-08-31]
sE1X Y Axis Printed Parts/lulzbot-bearing_holder_v1.1.b.stl
43.0 x 25.5 x 34.0
