papabur/sE1X-10mm/sE1X X Axis Printed Parts/SE1X 10mm carriage.STL

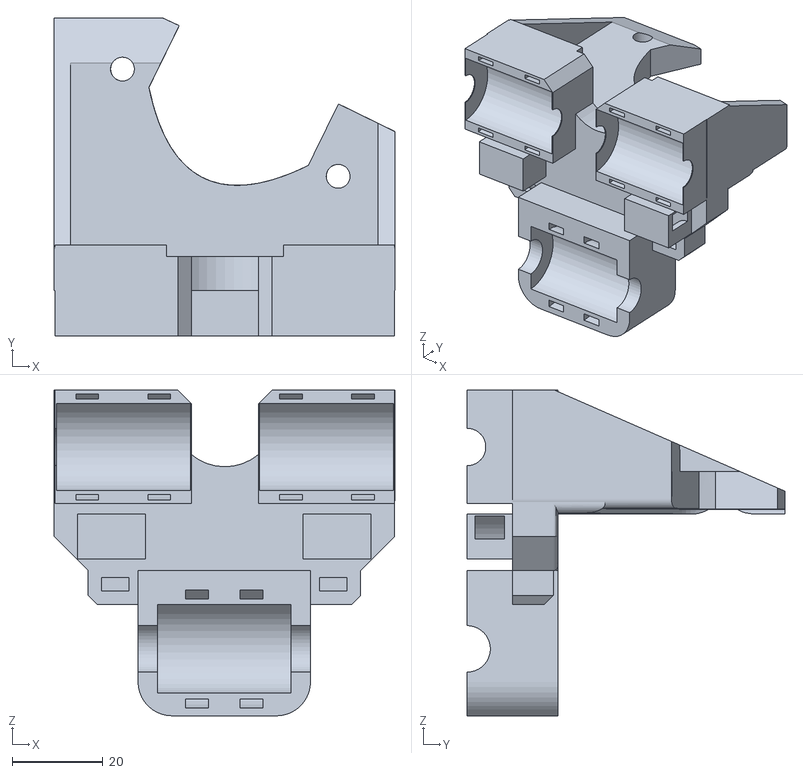
[picture p71: CAD file, 2015-07-30]
sE1X X Axis Printed Parts/SE1X 10mm carriage.STL
75.1 x 70.0 x 71.7
