papabur/sE1X-10mm/sE1X Y Axis Printed Parts/Lulz300x300_YGripper.stl

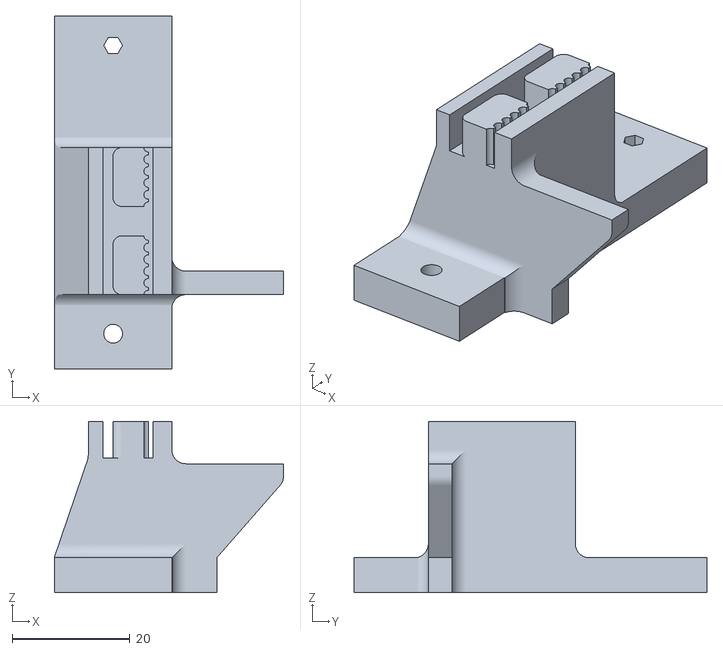
[picture p72: CAD file, 2015-08-31]
sE1X Y Axis Printed Parts/Lulz300x300_YGripper.stl
39.0 x 60.0 x 29.1
