papabur/sE1X-10mm/sE1X Y Axis Printed Parts/sE1X Y axis 10mm smooth rod holders.SLDPRT

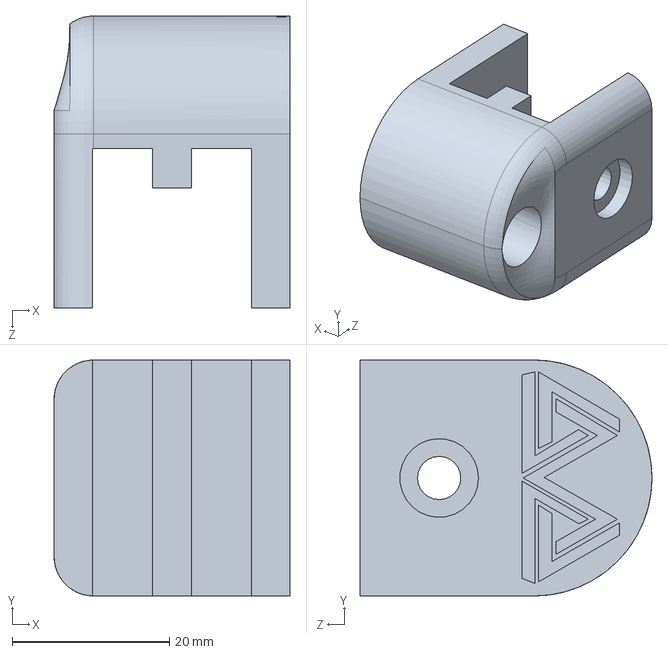
[picture p73: CAD file, 2015-07-30]
sE1X Y Axis Printed Parts/sE1X Y axis 10mm smooth rod holders.SLDPRT
30.0 x 30.0 x 37.1 mm
