papabur/sE1X-10mm/sE1X X Axis Printed Parts/sE1X X idler belt tensioner plate.SLDPRT

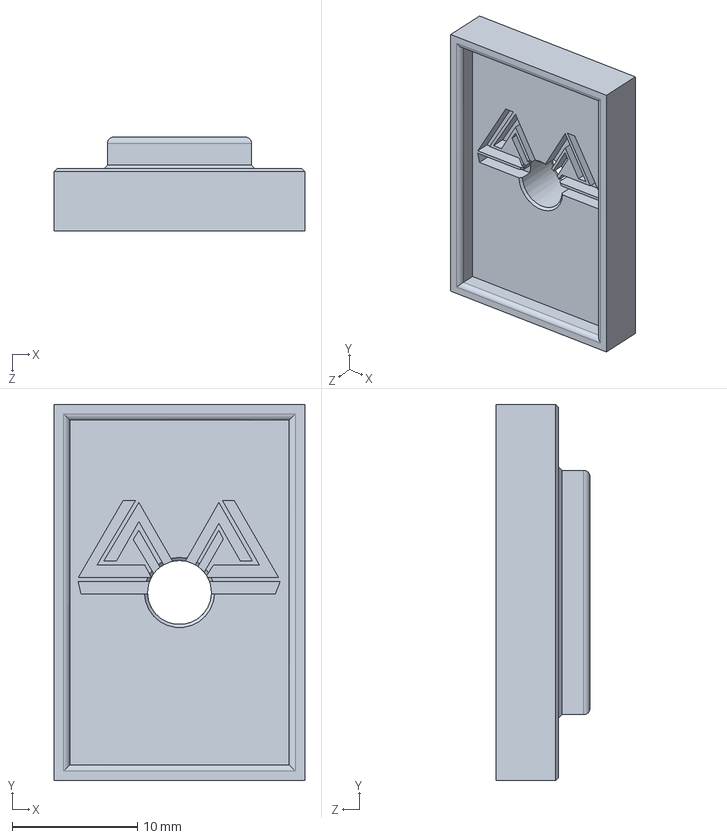
[picture p74: CAD file, 2015-07-30]
sE1X X Axis Printed Parts/sE1X X idler belt tensioner plate.SLDPRT
20.0 x 30.0 x 7.50 mm
