papabur/sE1X-10mm/sE1X Y Axis Printed Parts/sE1X corner brackets(TOP).SLDPRT

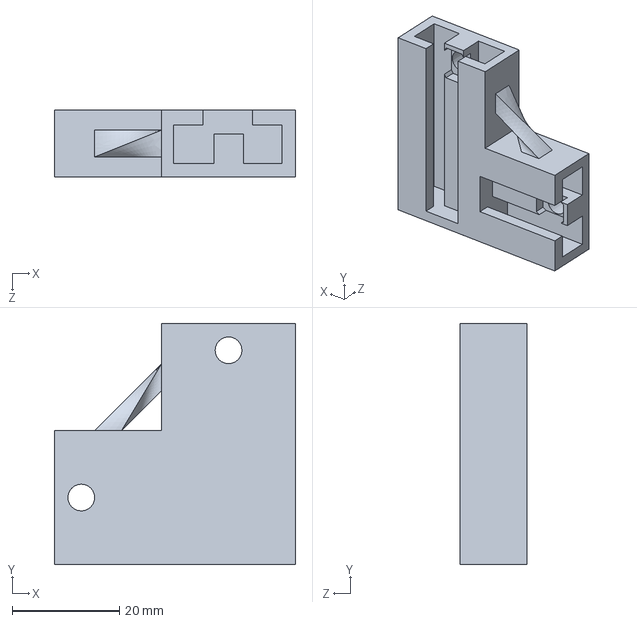
[picture p75: CAD file, 2015-06-30]
sE1X Y Axis Printed Parts/sE1X corner brackets(TOP).SLDPRT
45.0 x 45.0 x 12.5 mm
