papabur/sE1X-10mm/sE1X X Axis Printed Parts/SE1X 8mm carriage.SLDPRT

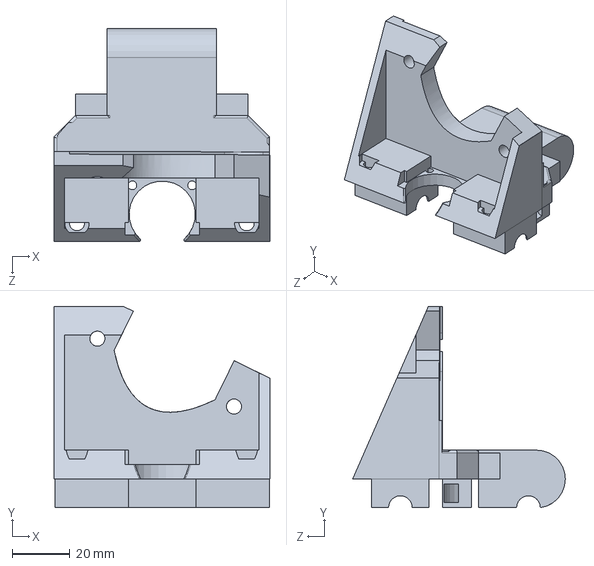
[picture p76: CAD file, 2015-07-30]
sE1X X Axis Printed Parts/SE1X 8mm carriage.SLDPRT
75.1 x 70.0 x 73.9 mm
