papabur/sE1X-10mm/sE1X Y Axis Printed Parts/y-rod-holder-1.75mm add.stl

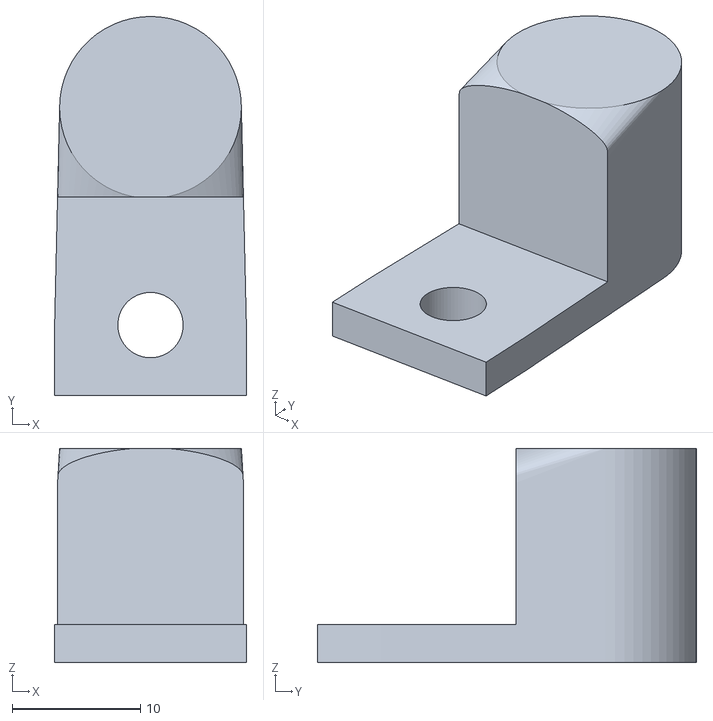
[picture p77: CAD file, 2015-05-10]
sE1X Y Axis Printed Parts/y-rod-holder-1.75mm add.stl
15.0 x 29.6 x 16.8
