papabur/sE1X-10mm/sE1X Y Axis Printed Parts/lulz-belt-gripper_5mm-pad.stl

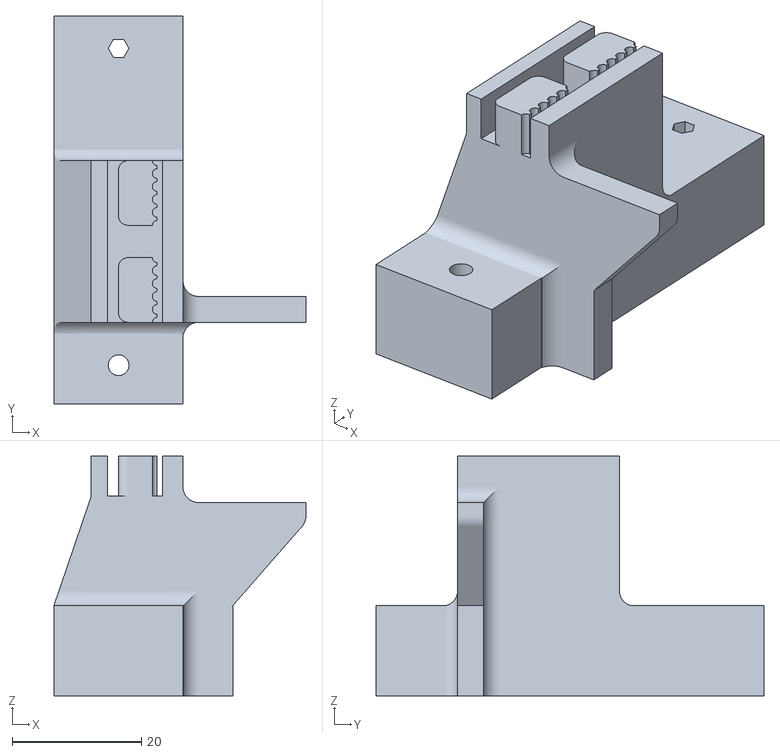
[picture p78: CAD file, 2015-05-10]
sE1X Y Axis Printed Parts/lulz-belt-gripper_5mm-pad.stl
39.0 x 60.0 x 37.1
